ikanoano/arty-videocap/hdl/PASS_THROUGH.v

`default_nettype none
`timescale 1 ps / 1 ps

module PASS_THROUGH #(
  parameter [4-1:0] RX_INV  = 4'b0110,
  parameter [4-1:0] TX_INV  = 4'b1100
) (
  input   wire          clk_src_raw,  // 100MHz
  input   wire          rst_raw_n,

  output  wire[4-1:0]     tmds_tx_p,
  output  wire[4-1:0]     tmds_tx_n,
  input   wire[4-1:0]     tmds_rx_p,
  input   wire[4-1:0]     tmds_rx_n,

  output  reg [3-1:0]     led0,     // RGB LEDs
  output  reg [3-1:0]     led1,     // RGB LEDs
  output  reg [3-1:0]     led2,     // RGB LEDs
  output  reg [3-1:0]     led3,     // RGB LEDs
  output  reg [5:4]       led,      // LEDs LD4-5
  input   wire[4-1:0]     btn,
  input   wire[4-1:0]     sw,

  // if use PASS_THROUGH as a TOP, comment out below
  output  wire            clk_data,
  output  wire            rst_data,
  output  wire            valid_data,
  output  wire[30-1:0]    data
);
wire  rst_ref, rst_des, rst_g, rst_ser, rst_idly;

// clocking (Create these modules using clocking wizard in vivado, MANUALLY!)
wire
  clk, locked_ref, clk1x,
  clk5x_des_nb, clk1x_des, clk5x_des, locked_des,
  clk5x_ser_nb, clk1x_ser, clk5x_ser, locked_ser;

// reference clock
clk_wiz_0 clocking (          // PLL
  .clk_in1(clk_src_raw),      // 100 MHz
  .reset(1'b0),
  .clk_out1(clk),             // 200 MHz, BUFG
  .locked(locked_ref)
);

// deserializer clock
clk_wiz_1 clocking_des (      // MMCM
  .clk_in1_p(tmds_rx_p[3]),   // X MHz,   Diff clock capable pin
  .clk_in1_n(tmds_rx_n[3]),
  .reset(rst_ref),
  .clk_out1(clk1x),           // X MHz,   BUFG
  .clk_out2(clk5x_des_nb),    // 5X MHz,  No buffer
  .locked(locked_des)
);
BUFIO bufio_des (.I(clk5x_des_nb), .O(clk5x_des));  // buffer for high freq
BUFR #(.BUFR_DIVIDE("5"),.SIM_DEVICE("7SERIES")) bufr_des (
  .I(clk5x_des_nb), .O(clk1x_des), .CE(1'b1), .CLR(1'b0));

// serializer clock
clk_wiz_2 clocking_ser (      // MMCM
  .clk_in1(clk1x),            // X MHz,   No buffer
  .reset(rst_ref),
  .clk_out1(),                // X MHz,   BUFG
  .clk_out2(clk5x_ser_nb),    // 5X MHz,  No buffer
  .locked(locked_ser)
);
BUFIO bufio_ser (.I(clk5x_ser_nb), .O(clk5x_ser));  // buffer for high freq
BUFR #(.BUFR_DIVIDE("5"),.SIM_DEVICE("7SERIES")) bufr_ser (
  .I(clk5x_ser_nb), .O(clk1x_ser), .CE(1'b1), .CLR(1'b0));

// resets
SASRESET sas_idly (
  .clk(clk), .sync_rst_src(1'b0),    .async_rst_src(~locked_ref), .rst(rst_idly));
SASRESET sas_ref (
  .clk(clk), .sync_rst_src(rst_idly),.async_rst_src(~rst_raw_n),  .rst(rst_ref));
SASRESET sas_des (
  .clk(clk1x_des), .sync_rst_src(rst_ref), .async_rst_src(~locked_des), .rst(rst_des));
SASRESET sas_g (
  .clk(clk1x),     .sync_rst_src(rst_ref), .async_rst_src(~locked_des), .rst(rst_g));
SASRESET sas_ser (
  .clk(clk1x_ser), .sync_rst_src(rst_des), .async_rst_src(~locked_ser), .rst(rst_ser));

// receiver
wire[3-1:0]   vld_cb, rdy_cb, dbg_pBitslip;
wire[30-1:0]  ch_des;
generate genvar gi;
for (gi = 0; gi < 3; gi = gi + 1) begin
  TMDS_Receiver # (
    .kCtlTknCount    (128),
    .kTimeoutMs      (50),
    .kRefClkFrqMHz   (200),       // what is the RefClk frequency
    .kIDLY_TapValuePs(78),        // delay in ps per tap
    .kIDLY_TapWidth  (5),         // number of bits for IDELAYE2 tap counter
    .kInvert         (1'b0)       // invert input
  ) rx (
    .PixelClk(clk1x_des),
    .SerialClk(clk5x_des),
    .RefClk(clk),
    .aRst(~locked_des),
    .pRst(rst_des),

    // Encoded serial data
    .sDataIn_p(tmds_rx_p[gi]),
    .sDataIn_n(tmds_rx_n[gi]),

    // Parallel data
    .pDataInBnd(ch_des[10*gi +: 10]),

    // Status and debug
    .pMeVld(vld_cb[gi]),
    .dbg_pBitslip(dbg_pBitslip[gi])
  );
end
endgenerate

// cross over clock region
wire[30-1:0]  invmask = {{10{RX_INV[2]}}, {10{RX_INV[1]}}, {10{RX_INV[0]}}};
wire          full1, empty1, filled1, full2, empty2;
reg           enqueue, dequeued;
wire[30-1:0]  ch_g,  ch_ser;
reg [30-1:0]  rch_des, rch_g, rch_ser;
reg [40-1:0]  irch_ser;

// clk1x_des -> clk1x
always @(posedge clk1x_des) rch_des <= ch_des ^ invmask;
always @(posedge clk1x_des) enqueue <= ~filled1;
ASYNC_FIFO #(.SIZE_SCALE(8), .WIDTH(30), .FILLED_THRESH(2**7)) cdc_fifo1 (
  .rst(rst_des),
  // Write clock region
  .wclk(clk1x_des),
  .full(full1),
  .filled_w(filled1),
  .enqueue(enqueue),
  .wdata(rch_des),
  // Read clock region
  .rclk(clk1x),
  .empty(empty1),
  .filled_r(),
  .dequeue(~empty1),
  .rdata(ch_g)
);

// clk1x -> clk1x_ser
always @(posedge clk1x) rch_g <= ch_g;
always @(posedge clk1x) dequeued <= ~empty1;
ASYNC_FIFO #(.SIZE_SCALE(8), .WIDTH(30), .FILLED_THRESH(2**7)) cdc_fifo2 (
  .rst(rst_g),
  // Write clock region
  .wclk(clk1x),
  .full(full2),
  .filled_w(),
  .enqueue(dequeued),
  .wdata(rch_g),
  // Read clock region
  .rclk(clk1x_ser),
  .empty(empty2),
  .filled_r(),
  .dequeue(~empty2),
  .rdata(ch_ser)
);

// invert data
always @(posedge clk1x_ser) begin
  rch_ser   <= ch_ser;
  irch_ser  <= {10'b0000011111, rch_ser} ^ {
      {10{TX_INV[3]}},
      {10{TX_INV[2]}},
      {10{TX_INV[1]}},
      {10{TX_INV[0]}}
    };
end

// sender
wire  [4-1:0] serialized;
SERIALIZER10 tx [4-1:0] (
  .clk_parallel_sdr(clk1x_ser),
  .clk_serial_ddr(clk5x_ser),
  .rst(rst_ser),
  .parallel_in(irch_ser),
  .serial_out(serialized)
);
OBUFDS #(.IOSTANDARD("TMDS_33")) tmdsbuf [4-1:0] (
  .O(tmds_tx_p),
  .OB(tmds_tx_n),
  .I(serialized)
);

// sniff
assign  clk_data  = clk1x;
assign  rst_data  = rst_g;
assign  valid_data= dequeued;
assign  data      = rch_g;

// IDELAY calibrator
wire        ideready;
IDELAYCTRL idc (
  .RDY(ideready),
  .REFCLK(clk),
  .RST(rst_idly)
);

// indicator
localparam[18-1:0]  LEDCNT_TH1  = (1<<18) - (1<<13);
localparam[18-1:0]  LEDCNT_TH2  = (1<<18) - (1<<10);
reg [18-1:0]  ledcnt1=0, ledcnt2=0;
always @(posedge clk) begin
  ledcnt1 <= ledcnt1+1;
  led[4]  <= ledcnt1<LEDCNT_TH1 ? 0 : locked_des;
end
always @(posedge clk1x_des) begin
  ledcnt2 <= ledcnt2+1;
  led[5]  <= ledcnt2<LEDCNT_TH1 ? 0 : &vld_cb;
  led0[2] <= ledcnt2<LEDCNT_TH2 ? 0 : vld_cb[0]; // Blue Channel
  led1[1] <= ledcnt2<LEDCNT_TH2 ? 0 : vld_cb[1]; // Green Channel
  led2[0] <= ledcnt2<LEDCNT_TH2 ? 0 : vld_cb[2]; // Red Channel
  led3    <= ledcnt2<LEDCNT_TH2 ? 0 : {dbg_pBitslip[0], dbg_pBitslip[1], dbg_pBitslip[2]};
end

// debug
(* keep = "true" *)
reg [6-1:0] dbg_bs_cnt[0:3-1];
always @(posedge clk1x_des) begin
  dbg_bs_cnt[0] <= rst_des ? 6'd0 : dbg_bs_cnt[0] + dbg_pBitslip[0];
  dbg_bs_cnt[1] <= rst_des ? 6'd0 : dbg_bs_cnt[1] + dbg_pBitslip[1];
  dbg_bs_cnt[2] <= rst_des ? 6'd0 : dbg_bs_cnt[2] + dbg_pBitslip[2];
end

initial if(RX_INV[3]) begin $display("not supported RX_INV"); $finish(); end
endmodule

`default_nettype wire
